n6dlh/7920-GPU-Server-Conversion/ESP32 Code and Cooling/images/image-1.png

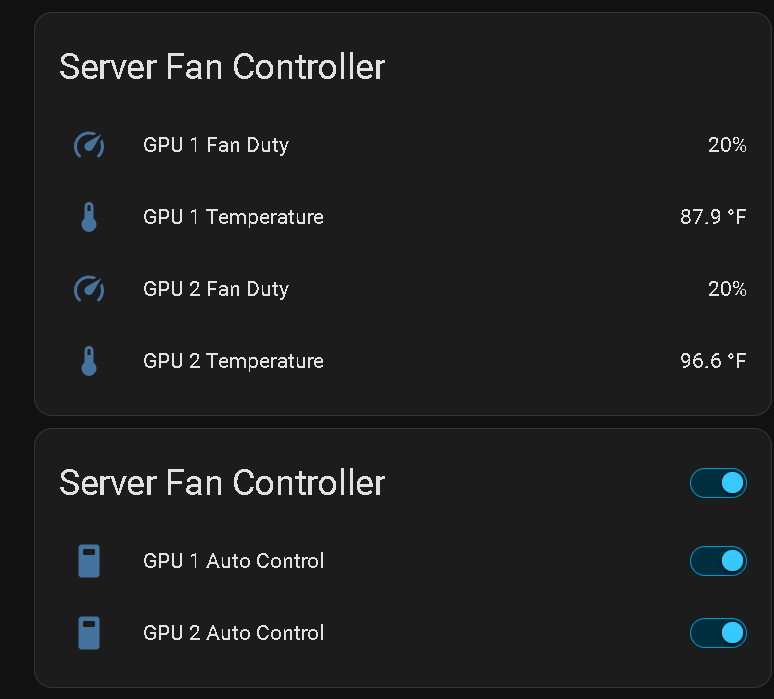
ESP32 Code and Cooling/images/image-1.png
