n6dlh/7920-GPU-Server-Conversion/Pictures/IMG_4344.JPG

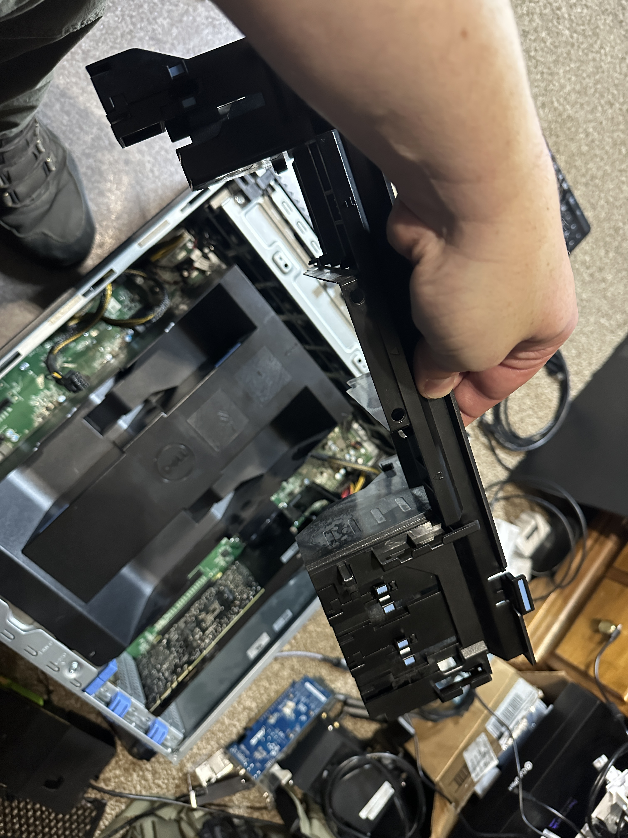
Pictures/IMG_4344.JPG
