n6dlh/7920-GPU-Server-Conversion/Pictures/IMG_4345.jpg

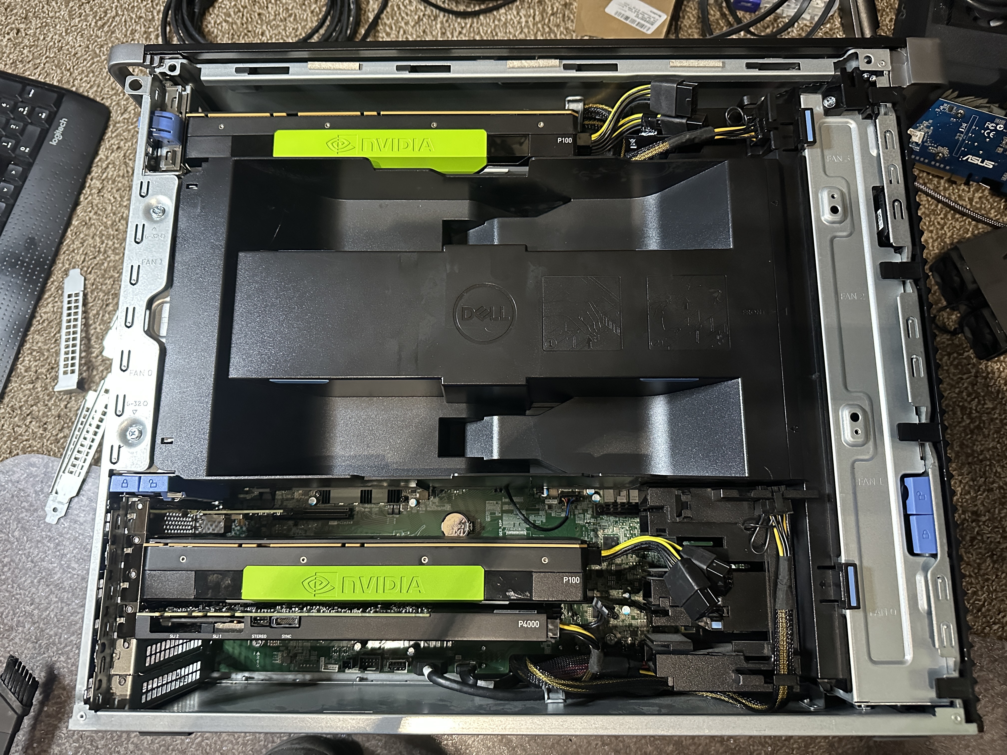
Pictures/IMG_4345.jpg
