n6dlh/7920-GPU-Server-Conversion/Pictures/IMG_4542.jpg

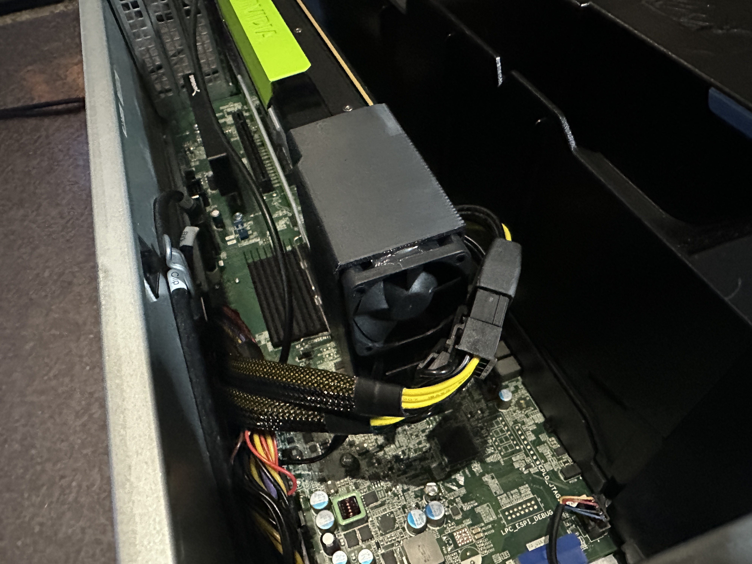
Pictures/IMG_4542.jpg
